mtinet/smartFarm/0. pico_test/6. OLED/moveHammer.py

# This code was written by Juhyun Kim.

from machine import Pin, I2C
from ssd1306 import SSD1306_I2C
import framebuf

i2c = I2C(0, sda=Pin(16), scl=Pin(17), freq=200000)
oled = SSD1306_I2C(128, 64, i2c)
TH = bytearray(b'\x00\x00\x00\x00\x00\x00\x00\x00\x00\x00\x00\x00\x00\x00\x00\x00\x00\x00\x00\x00\x00\x00\x00\x00\x00\x00\x00\x00\x00\x00\x00\x00\x00\x00\x00[P\x00\x00\x00\x00\x00\x03\xad\xec\x0f\x00\x00\x00\x00\rv\xb6\x1a\x80\x00\x00\x00\x16\xdb[m\x80\x00\x00\x00um\xb5\xb6\x80\x00\x00\x00[\xb5n\xdb\x00\x00\x00\x01\xadW\xb5m\x80\x00\x00\x01w\xed[\xb6\x80\x00\x00\x03\xa8\x1a\xec+\x00\x00\x00\x05@\x17P\x1d\x00\x00\x00\x0e\x00\r\xb0\x06\x80\x00\x00\x08\x00\n\xd0\x00\x00\x00\x00\x08\x00\x17`\x00\x00\x00\x00\x00\x00\x00\x00\x00\x00\x00\x00\x00\x00\x00\x00\x00\x00\x00\x00\x00\x00\x00\x00\x00\x00\x00\x00\x00\x00\x00@\x00\x00\x00\x00\x00\x00\x1f\xa0\x00\x00\x00\x00\x00\x00\n\xd0\x00\x00\x00\x00\x00\x00\r`\x00\x00\x00\x00\x00\x00\x17\xb0\x00\x00\x00\x00\x00\x00\n\xd0\x00\x00\x00\x00\x00\x00\x1b`\x00\x00\x00\x00\x00\x00\r\xb0\x00\x00\x00\x00\x00\x00\x16\xa0\x00\x00\x00\x00\x00\x00\x0bp\x00\x00\x00\x00\x00\x00\x1d\xa0\x00\x00\x00\x00\x00\x00\n\xd0\x00\x00\x00\x00\x00\x00\x17p\x00\x00\x00\x00\x00\x00\x1a\xa0\x00\x00\x00\x00\x00\x00\r\xd0\x00\x00\x00\x00\x00\x00\x16\xb0\x00\x00\x00\x00\x00\x00\x1b`\x00\x00\x00\x00\x00\x00\r\xb0\x00\x00\x00\x00\x00\x00\x16\xd0\x00\x00\x00\x00\x00\x00\x1bp\x00\x00\x00\x00\x00\x00\r\xa8\x00\x00\x00\x00\x00\x00\x16\xb0\x00\x00\x00\x00\x00\x00\x1b`\x00\x00\x00\x00\x00\x00\x15\xb0\x00\x00\x00\x00\x00\x00\x1e\xd0\x00\x00\x00\x00\x00\x00\x13p\x00\x00\x00\x00\x00\x00\x1d\xa8\x00\x00\x00\x00\x00\x00\x16\xb0\x00\x00\x00\x00\x00\x00\x15\xd0\x00\x00\x00\x00\x00\x00\x1a\xb8\x00\x00\x00\x00\x00\x00\x17`\x00\x00\x00\x00\x00\x00\x1a\xd8\x00\x00\x00\x00\x00\x00\x17h\x00\x00\x00\x00\x00\x00\x1a\xb0\x00\x00\x00\x00\x00\x00\x1d\xd8\x00\x00\x00\x00\x00\x00+h\x00\x00\x00\x00\x00\x00\x16\xb0\x00\x00\x00\x00\x00\x00\x1b\xd8\x00\x00\x00\x00\x00\x00\x16`\x00\x00\x00\x00\x00\x00\x0b\xa0\x00\x00\x00\x00\x00\x00\x00\x00\x00\x00\x00\x00\x00\x00\x00\x00\x00\x00\x00\x00\x00\x00\x00\x00\x00\x00\x00\x00\x00\x00\x00\x00\x00\x00\x00')

fb = framebuf.FrameBuffer(TH,64,64, framebuf.MONO_HLSB)
oled.fill(0)
while True:
    for i in range(-64,128):
        oled.blit(fb,i,0)
        oled.show()
