mtinet/smartFarm/0. pico_test/2. analogSensor/lm35.py

# This code was written by Juhyun Kim.

import machine
import utime

analog_value = machine.ADC(27)
count = 0
conversion_factor = 3.3/65535 # based of 5v supply and 16 bit value

while True:
    # Read ADC value of sensor
    temp_voltage_raw = analog_value.read_u16()

    # Converts ADC value back to voltage
    convert_voltage = temp_voltage_raw*conversion_factor

    C_temp = convert_voltage/(10.0 / 1000)

    F_temp = (C_temp*9/5) +32

    print("raw voltage: ", temp_voltage_raw, "\t converted voltage: ",convert_voltage, "\t Temperature(C): ",C_temp, "\t Temperature(F): ",F_temp)
    count +=1
    utime.sleep(0.2)
