mtinet/smartFarm/0. pico_test/9. PWM/PWMRange.py

# This code was written by Juhyun Kim.

from machine import Pin, PWM
from time import sleep

pwm = PWM(Pin(1))

pwm.freq(1000)

while True:
    for duty in range(65025):
        pwm.duty_u16(duty)
        sleep(0.0001)
    for duty in range(65025, 0, -1):
        pwm.duty_u16(duty)
        sleep(0.0001)
