mtinet/smartFarm/0. pico_test/13. AHT10/aht10.py

# This code was written by Juhyun Kim. 

import utime
from machine import Pin, I2C

import ahtx0

# I2C for the Wemos D1 Mini with ESP8266
i2c = I2C(1, scl=Pin(15), sda=Pin(14), freq=200000)

# Create the sensor object using I2C
sensor = ahtx0.AHT10(i2c)

while True:
    print("\nTemperature: %0.2f C" % ((sensor.temperature)-5))
    print("Humidity: %0.2f %%" % sensor.relative_humidity)
    utime.sleep(1)
